EnviroDIY/LTEbee-Adapter/doc/images/LTEbee_adapter_bee_left.jpg

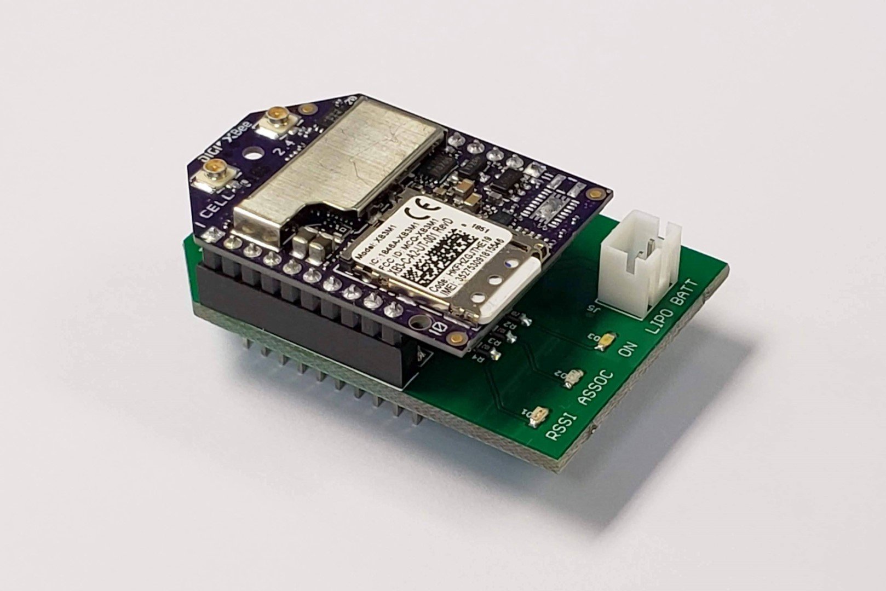
doc/images/LTEbee_adapter_bee_left.jpg
