EnviroDIY/LTEbee-Adapter/doc/images/LTEbee_adapter_mayfly_right.jpg

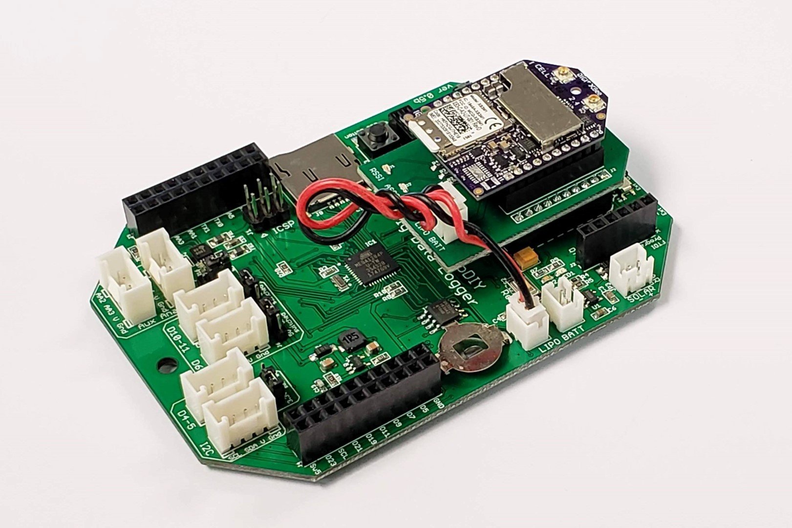
doc/images/LTEbee_adapter_mayfly_right.jpg
