EnviroDIY/LTEbee-Adapter/doc/images/LTEbee_r1_top.JPG

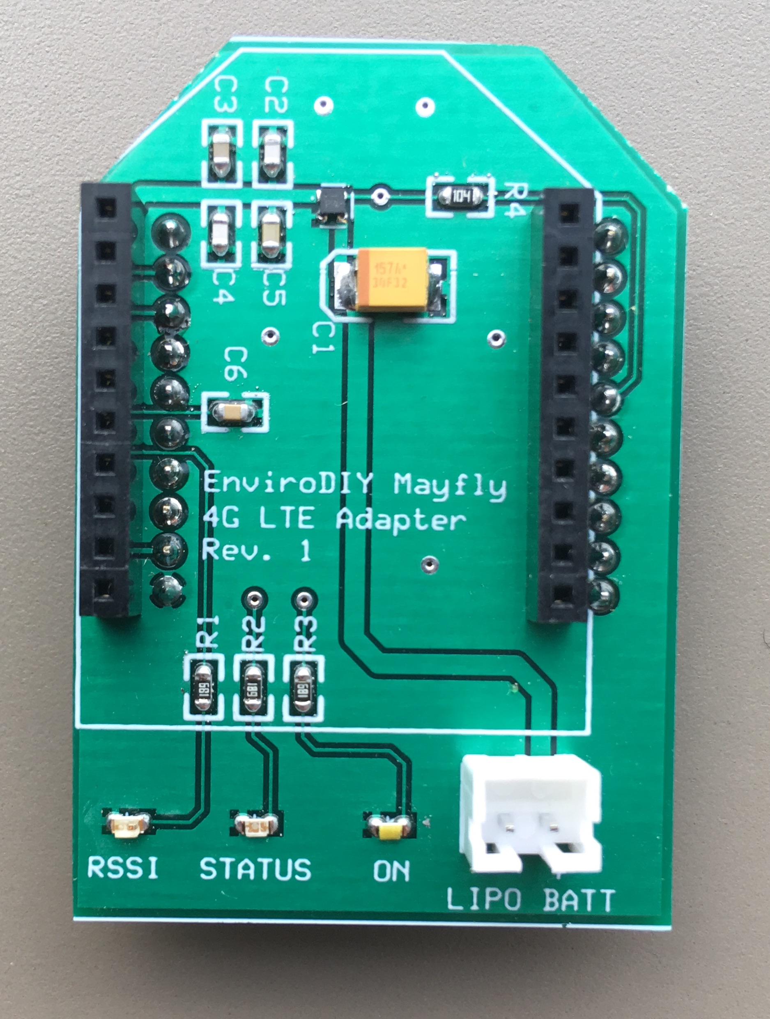
doc/images/LTEbee_r1_top.JPG
